Graf3x/PNY5080-Custom-Backplate/docs/writeup-img/02-e2e562962d.jpg

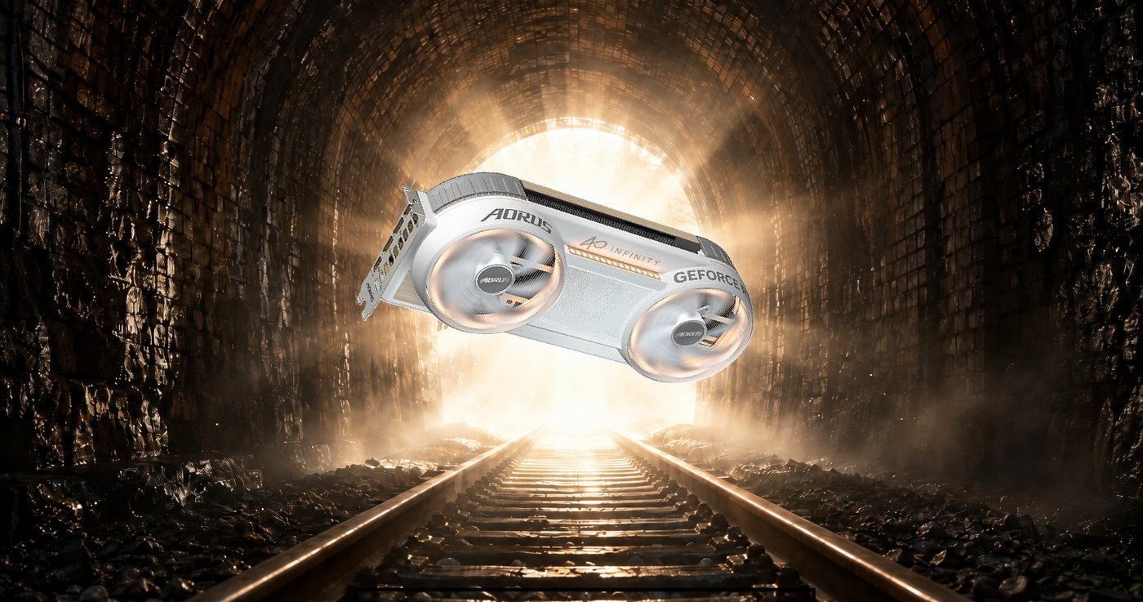
docs/writeup-img/02-e2e562962d.jpg
