Graf3x/PNY5080-Custom-Backplate/docs/writeup-img/03-cdf34074a6.jpg

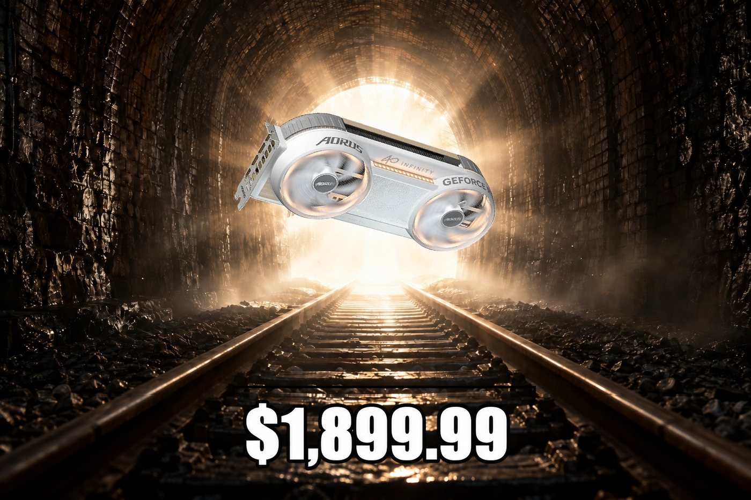
docs/writeup-img/03-cdf34074a6.jpg
