Graf3x/PNY5080-Custom-Backplate/docs/writeup-img/05-996a30fa68.png

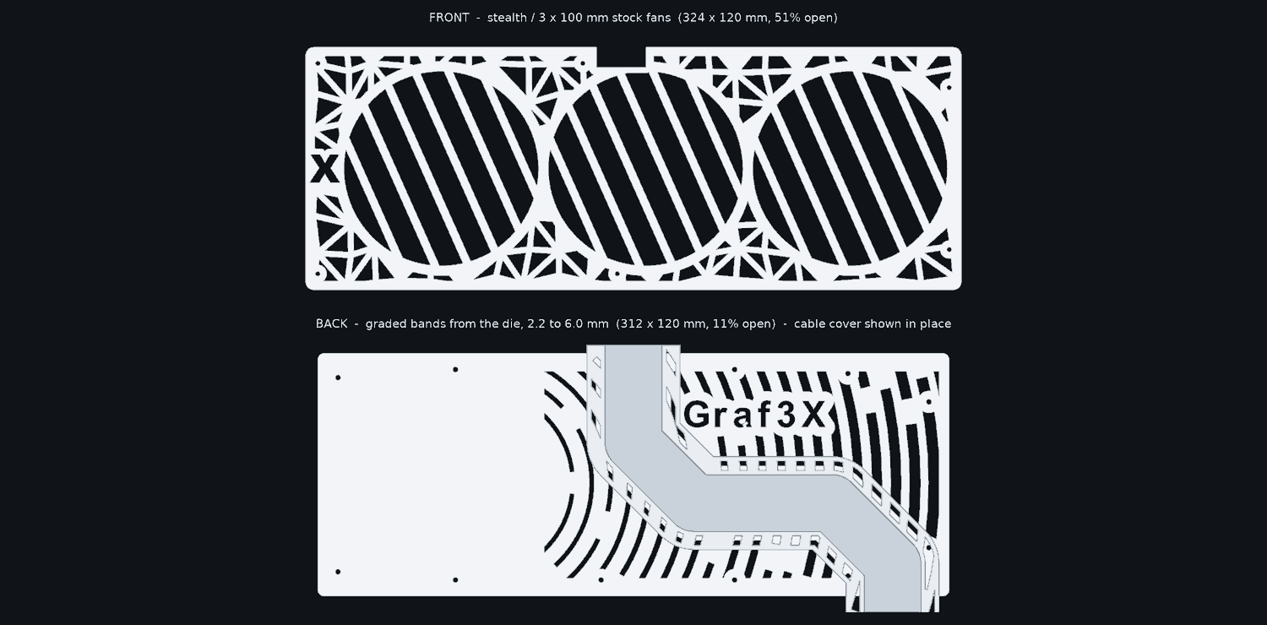
docs/writeup-img/05-996a30fa68.png
