Graf3x/PNY5080-Custom-Backplate/docs/writeup-img/07-0955286835.jpg

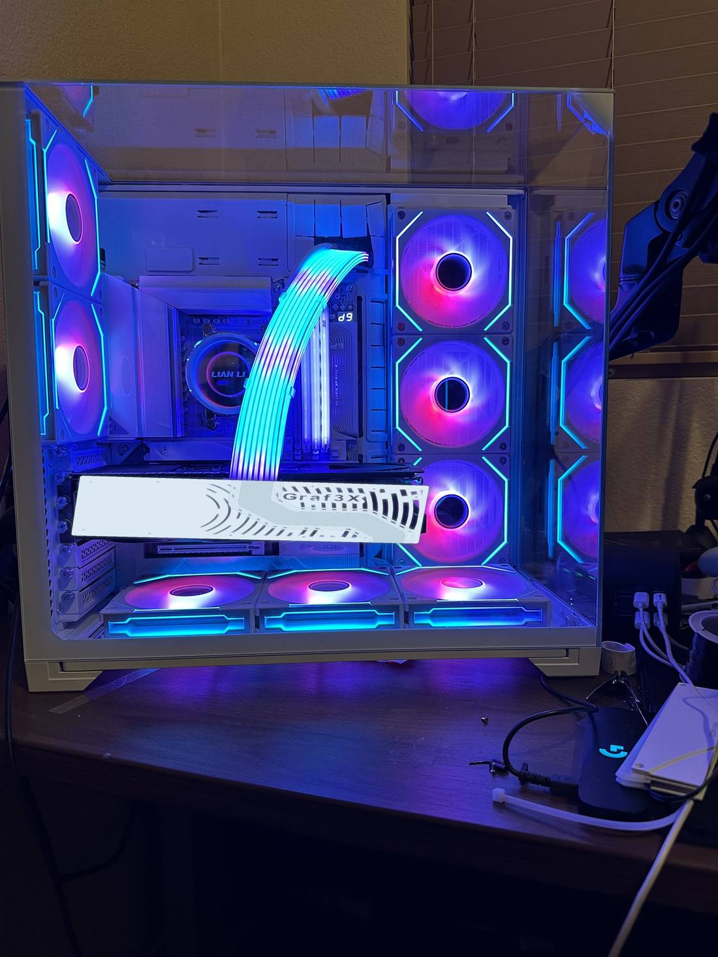
docs/writeup-img/07-0955286835.jpg
