Graf3x/PNY5080-Custom-Backplate/docs/writeup-img/08-942528947a.jpg

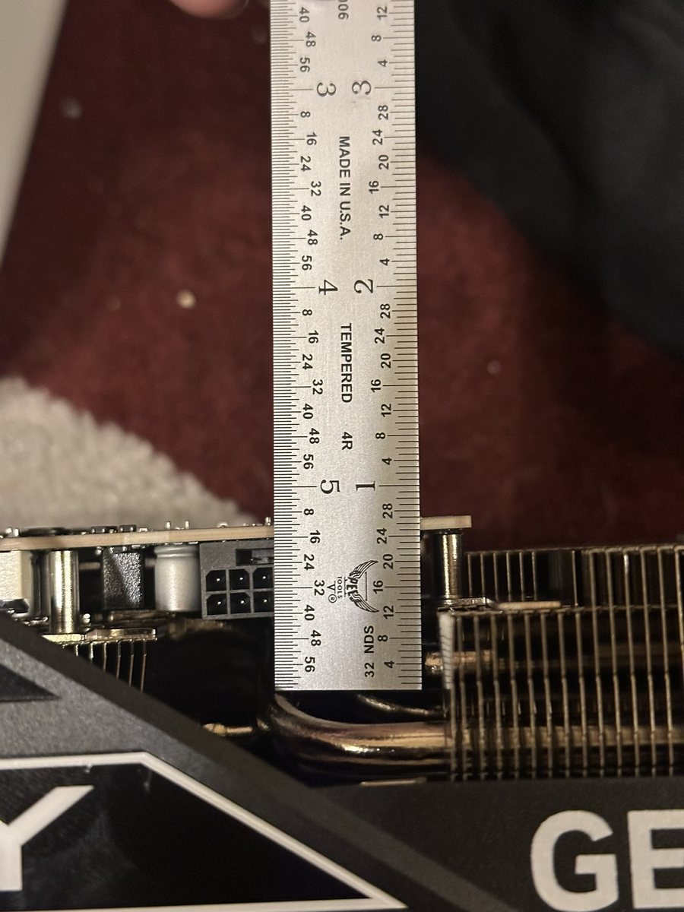
docs/writeup-img/08-942528947a.jpg
