Graf3x/PNY5080-Custom-Backplate/docs/writeup-img/09-984eafe323.png

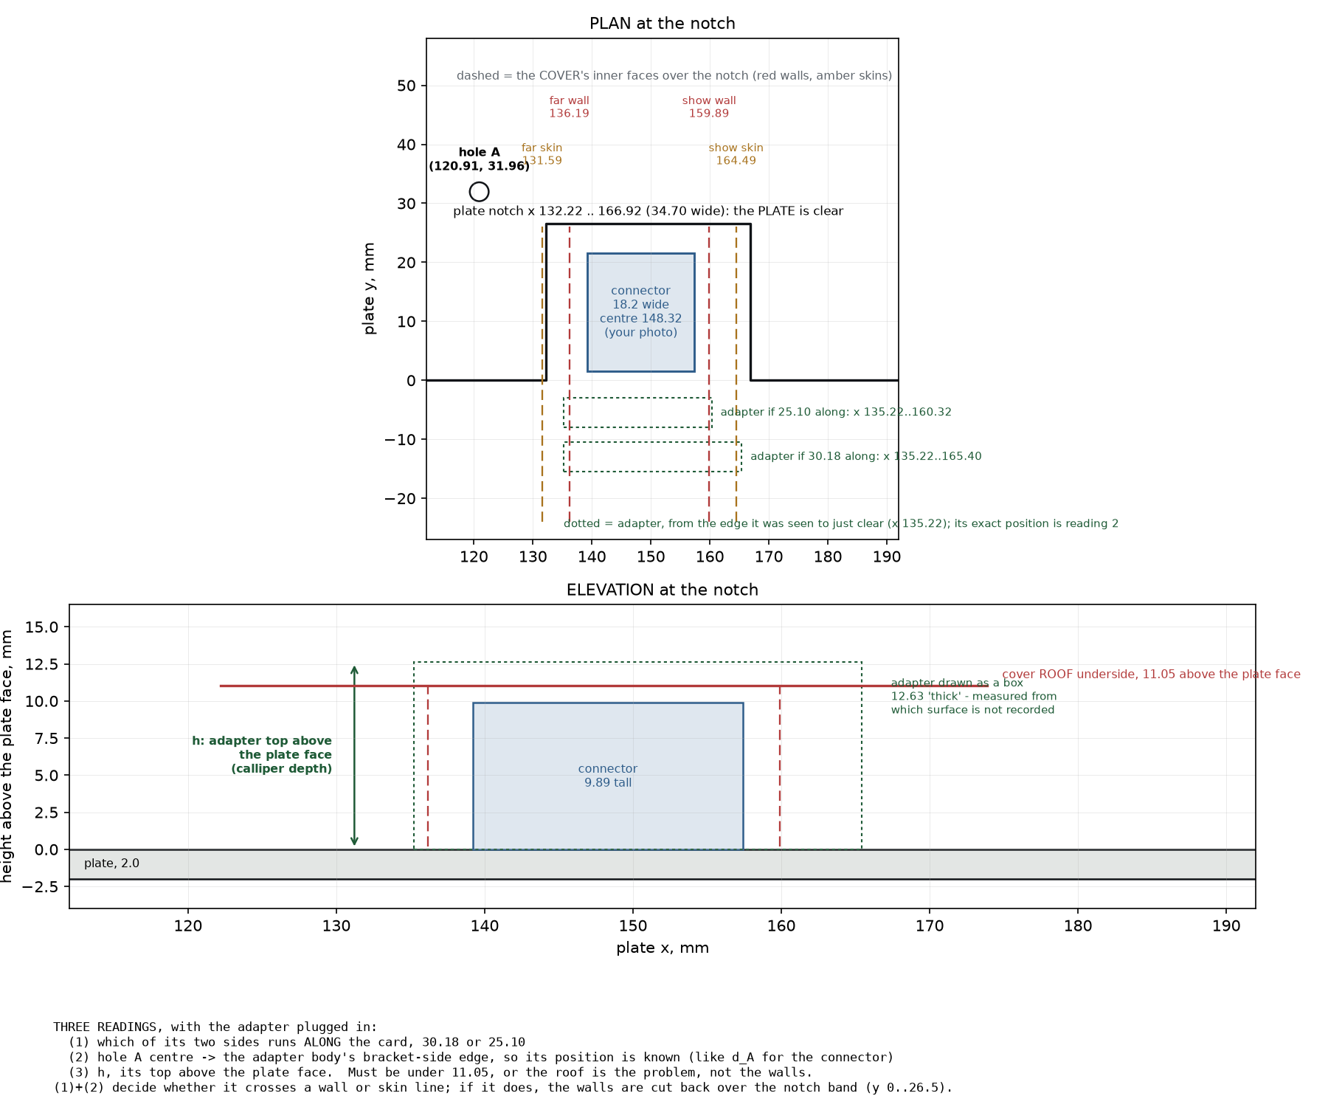
docs/writeup-img/09-984eafe323.png
