Graf3x/PNY5080-Custom-Backplate/docs/writeup-img/11-cb252d46e1.jpg

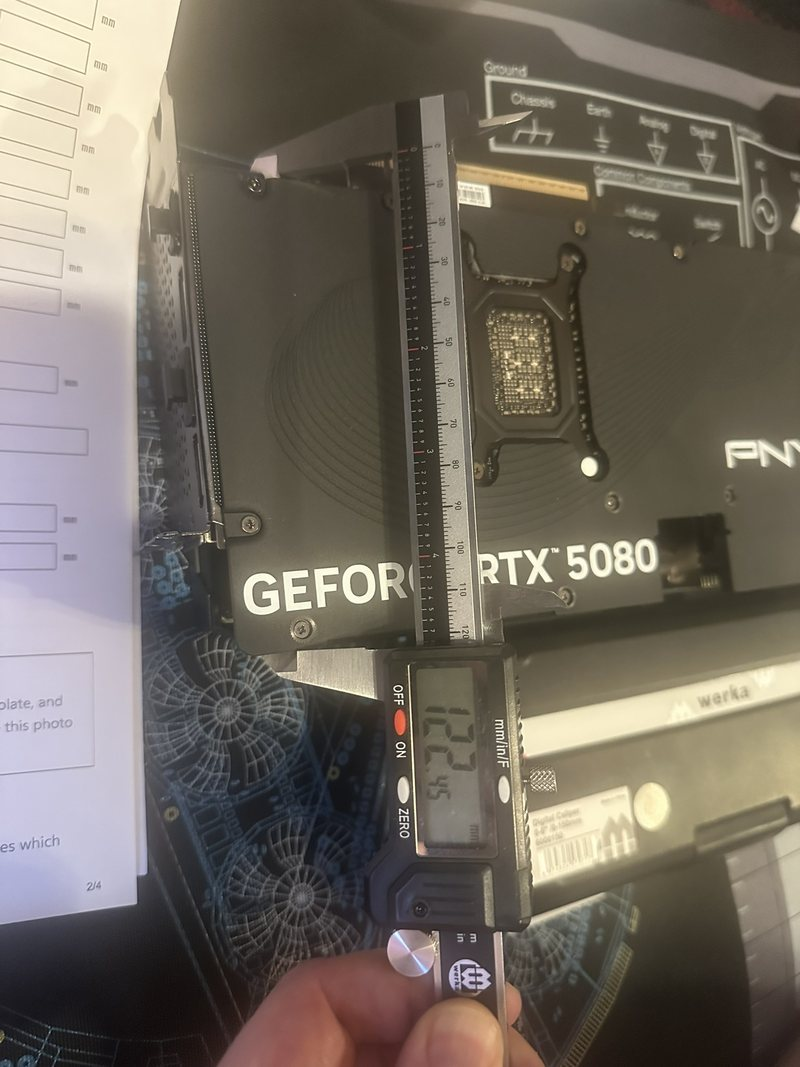
docs/writeup-img/11-cb252d46e1.jpg
