Graf3x/PNY5080-Custom-Backplate/docs/writeup-img/12-ec8e2748a8.jpg

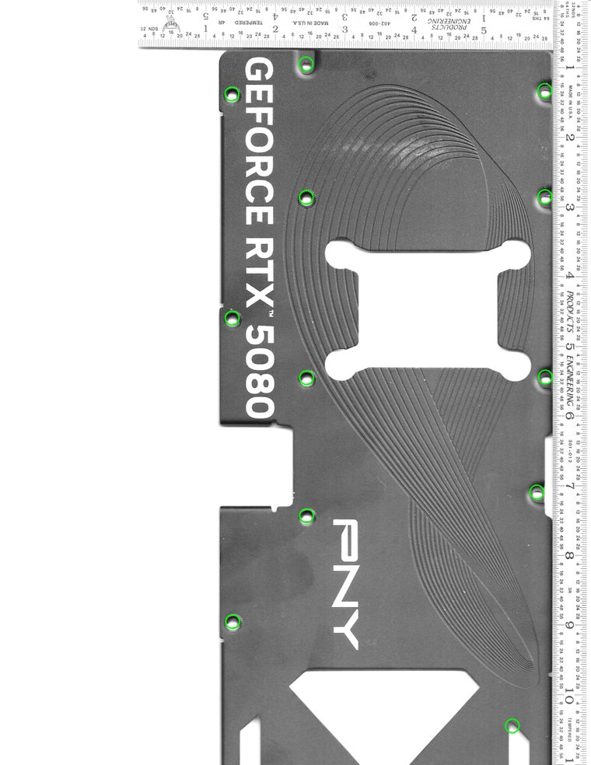
docs/writeup-img/12-ec8e2748a8.jpg
