Graf3x/PNY5080-Custom-Backplate/docs/writeup-img/13-f72fab094b.jpg

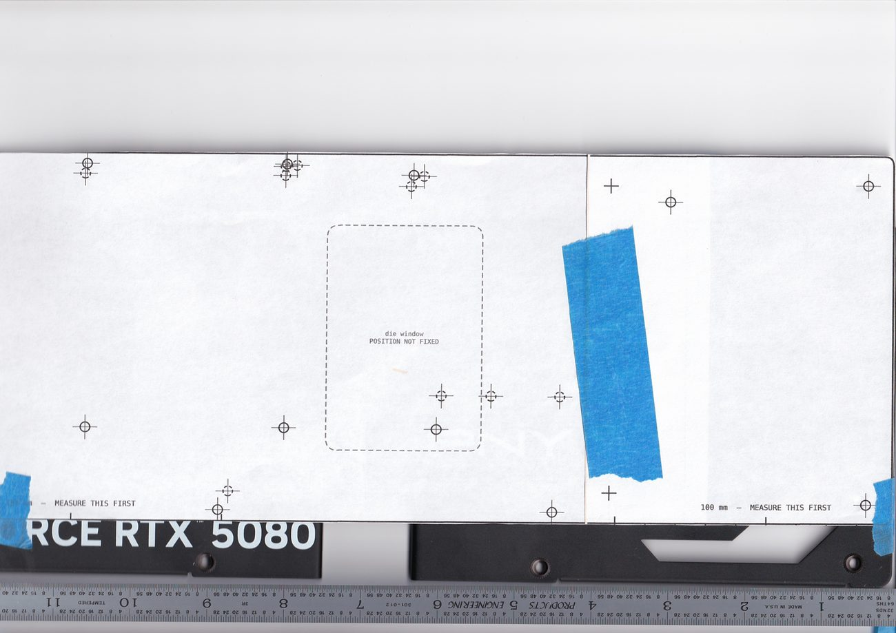
docs/writeup-img/13-f72fab094b.jpg
