Graf3x/PNY5080-Custom-Backplate/docs/writeup-img/15-37b291bcfa.png

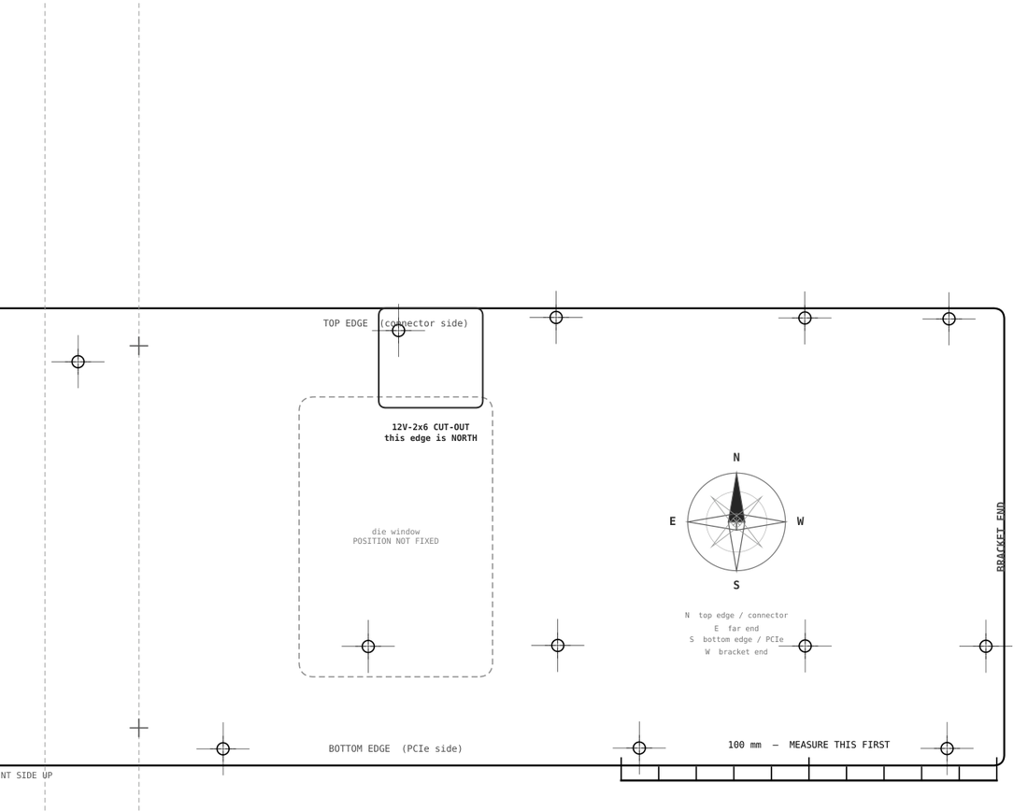
docs/writeup-img/15-37b291bcfa.png
