Graf3x/PNY5080-Custom-Backplate/docs/writeup-img/18-8b5d0298e2.png

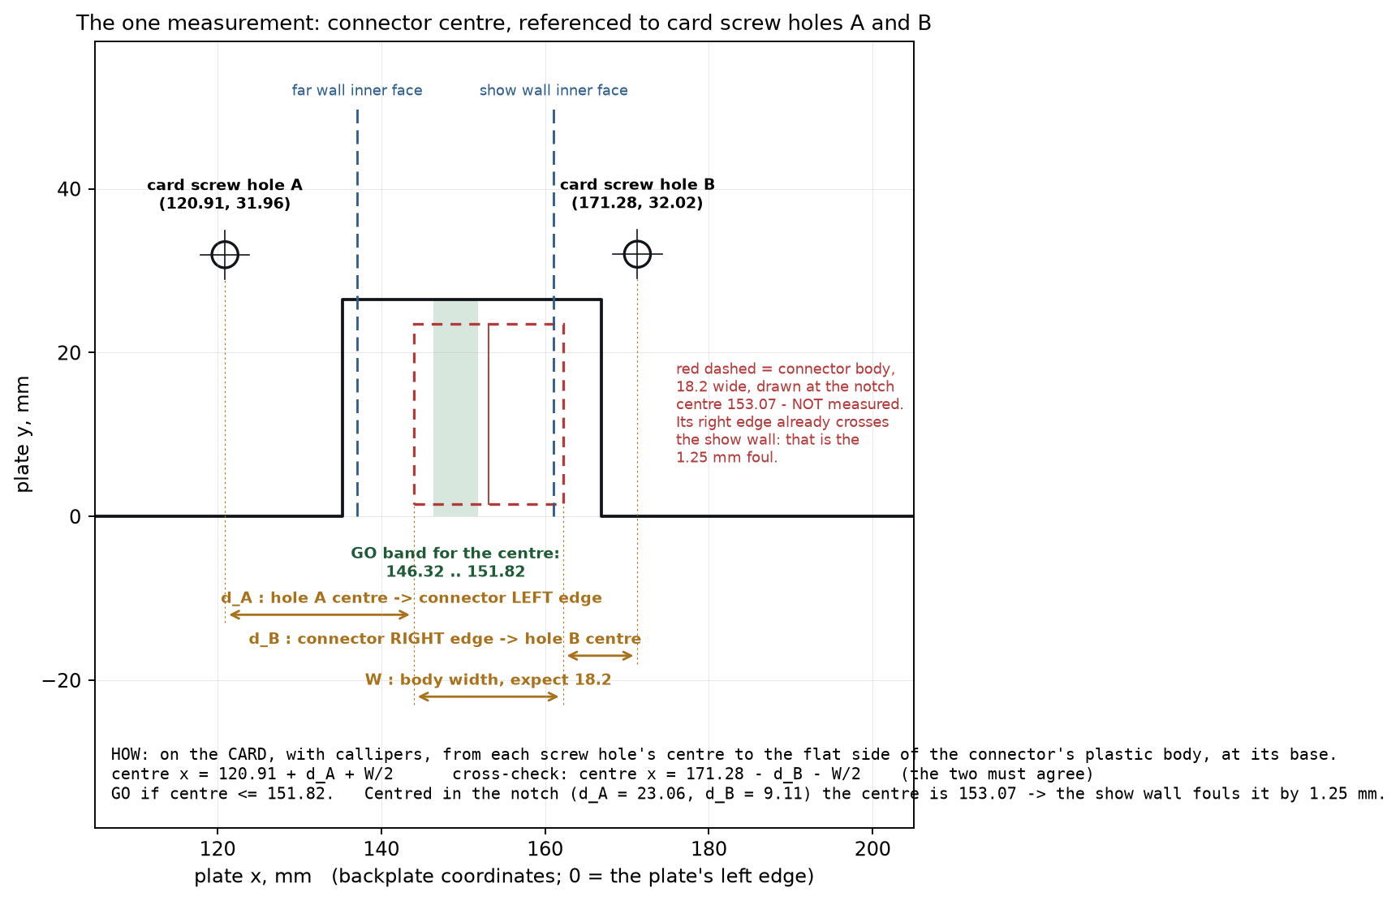
docs/writeup-img/18-8b5d0298e2.png
