Graf3x/PNY5080-Custom-Backplate/docs/writeup-img/19-ffc3acb33d.jpg

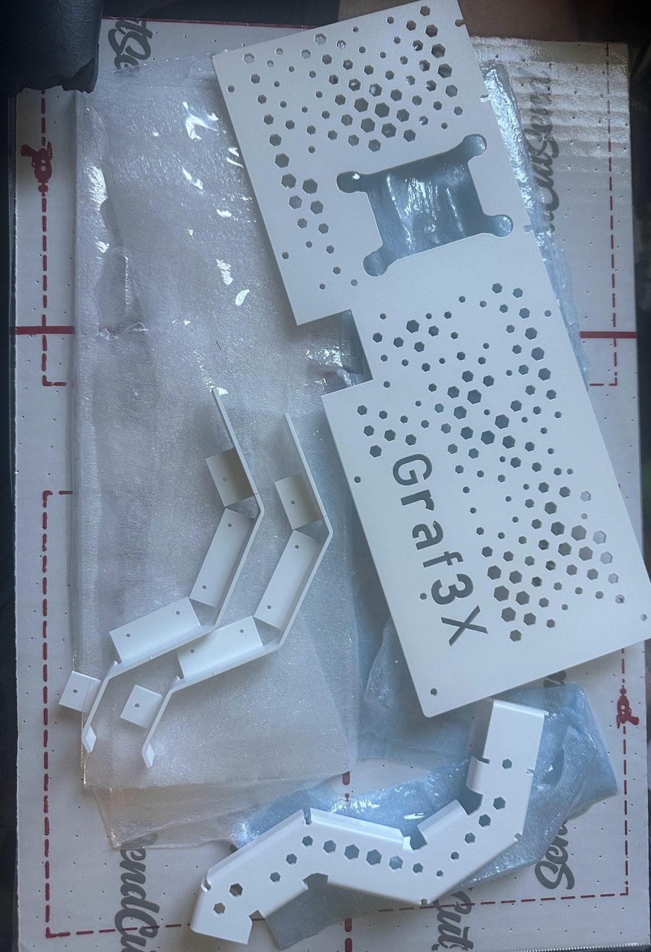
docs/writeup-img/19-ffc3acb33d.jpg
