Graf3x/PNY5080-Custom-Backplate/docs/writeup-img/20-1154d42b42.png

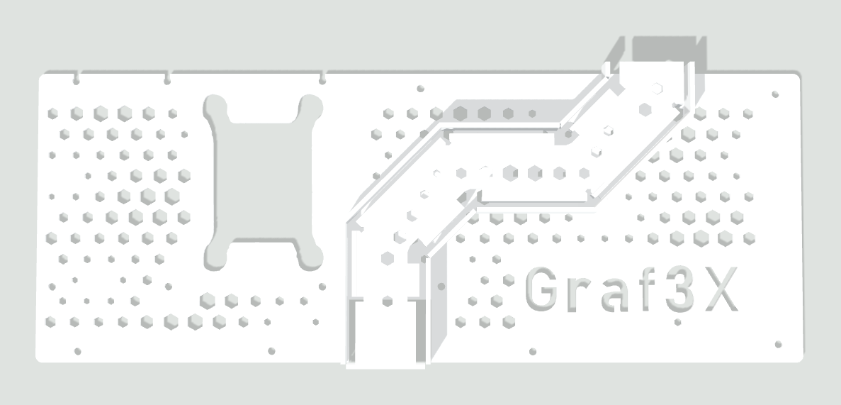
docs/writeup-img/20-1154d42b42.png
