Graf3x/PNY5080-Custom-Backplate/docs/writeup-img/21-436734db5e.png

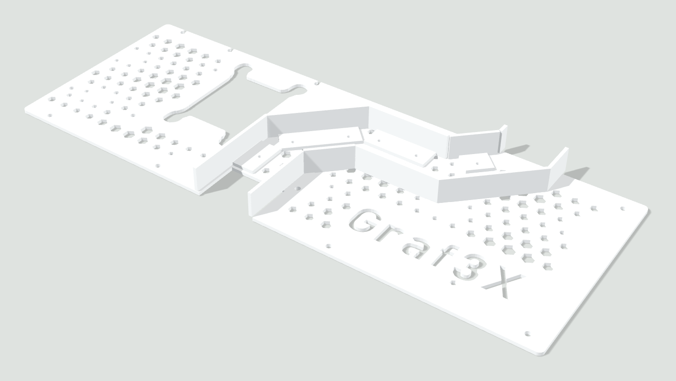
docs/writeup-img/21-436734db5e.png
