Graf3x/PNY5080-Custom-Backplate/docs/writeup-img/22-54fd710c02.png

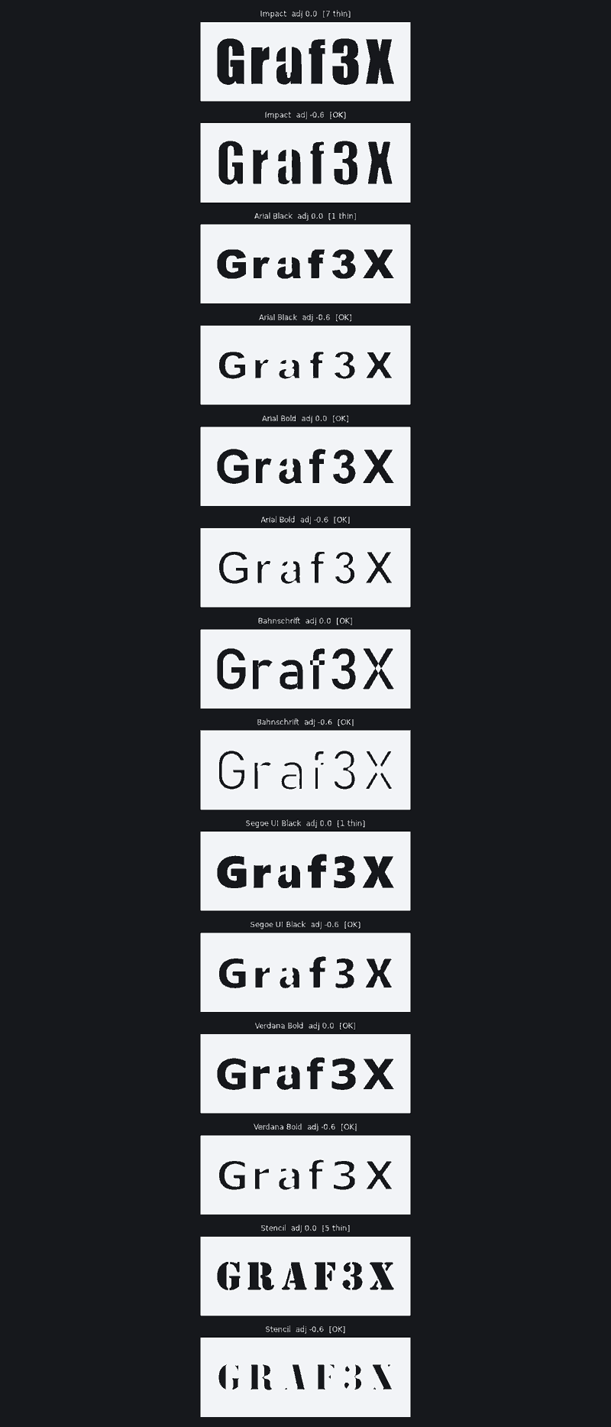
docs/writeup-img/22-54fd710c02.png
