Graf3x/PNY5080-Custom-Backplate/docs/writeup-img/23-59aad24f57.jpg

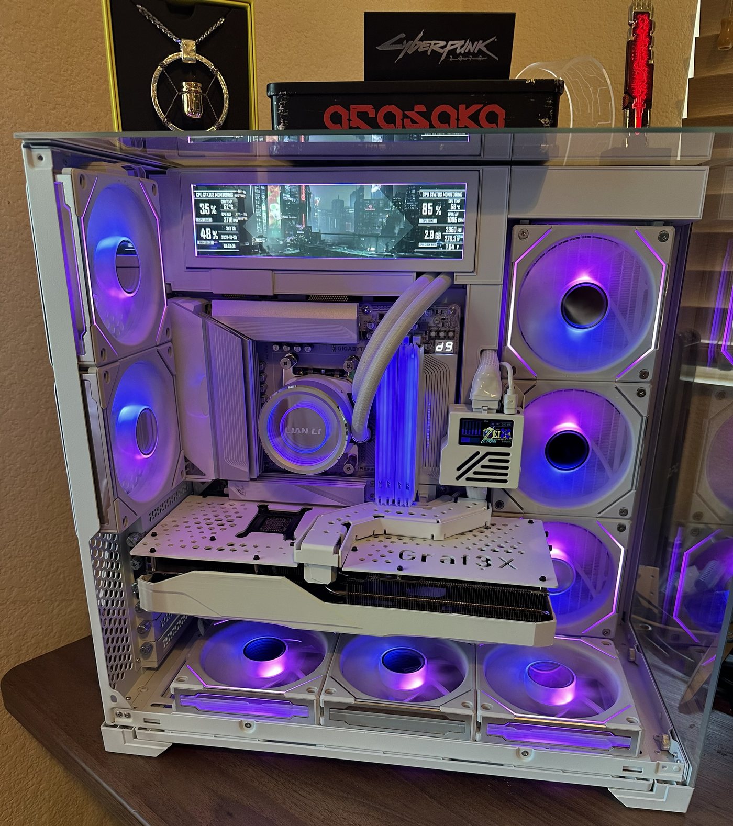
docs/writeup-img/23-59aad24f57.jpg
