Graf3x/PNY5080-Custom-Backplate/docs/writeup-img/24-b6ce1e3912.jpg

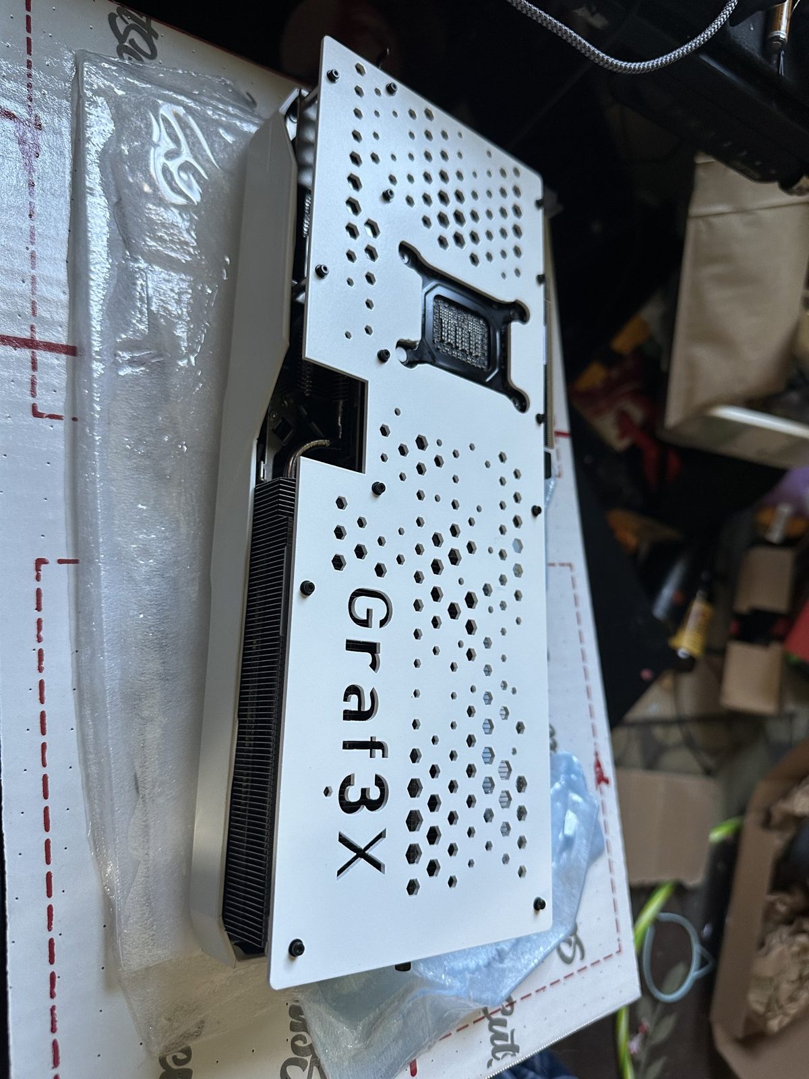
docs/writeup-img/24-b6ce1e3912.jpg
