Graf3x/PNY5080-Custom-Backplate/docs/writeup-img/25-e88f9072c6.jpg

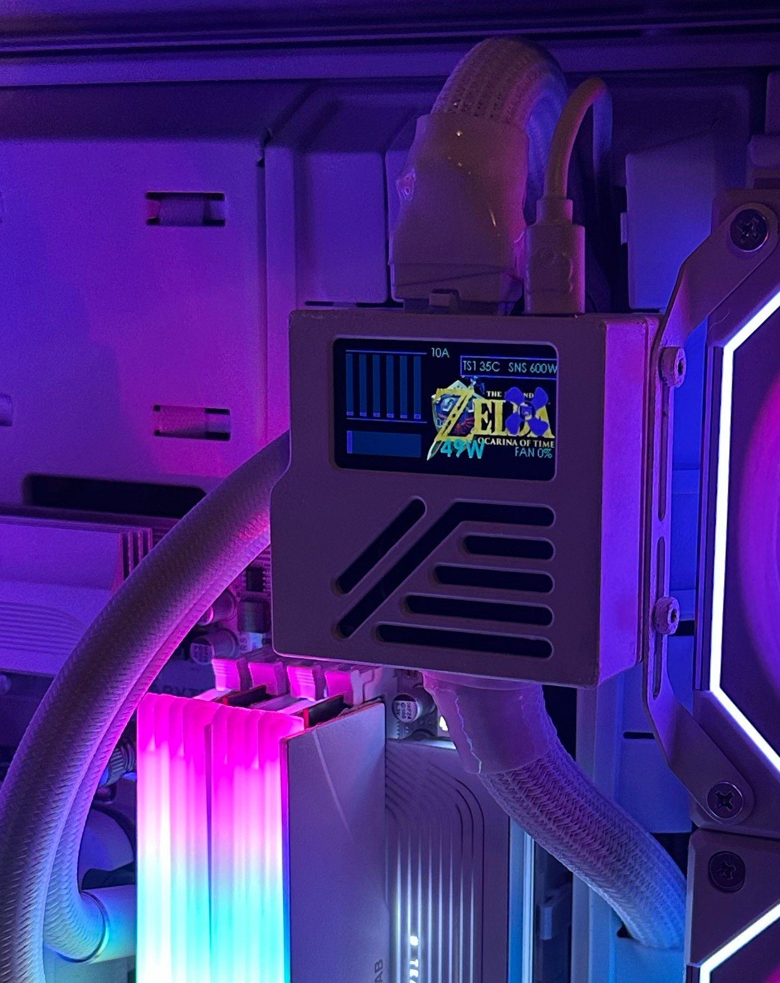
docs/writeup-img/25-e88f9072c6.jpg
