Graf3x/PNY5080-Custom-Backplate/reference/v94-as-ordered/skin_show_v94.dxf

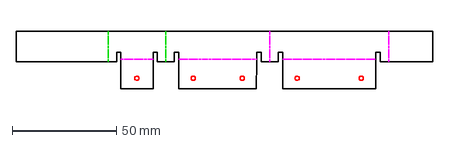
[picture p42: CAD file, 2026-10-07]
reference/v94-as-ordered/skin_show_v94.dxf
199.6 x 27.4 mm
