Graf3x/PNY5080-Custom-Backplate/docs/img/finished-build.jpg

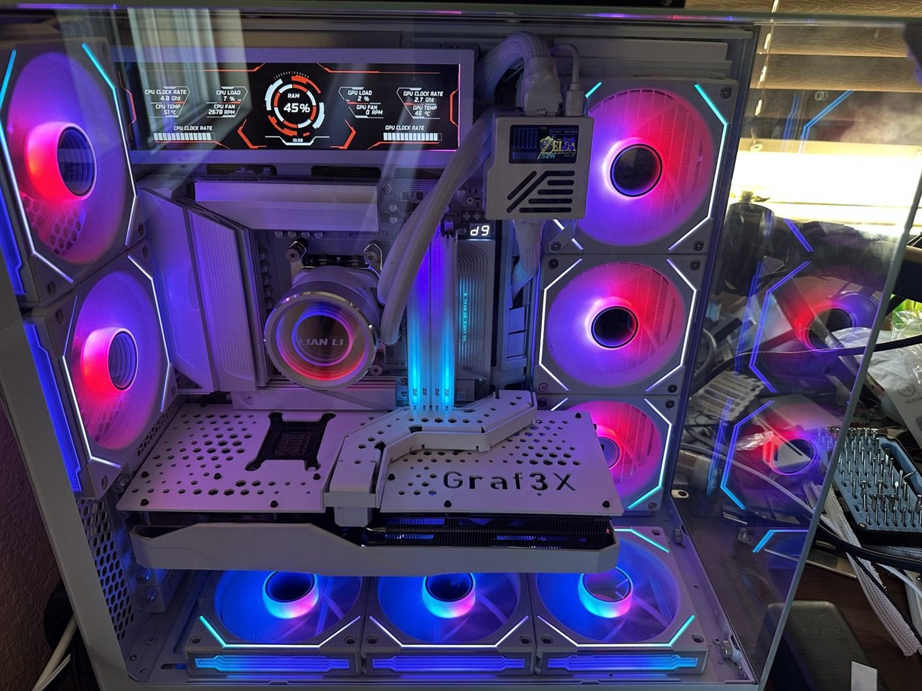
docs/img/finished-build.jpg
